0xMartin/TweenWave/Firmware/src/CommandLine.cpp

#include "CommandLine.h"

#include <SPIFFS.h>

CommandLine::CommandLine() {}

void CommandLine::RunSetup() {
  Serial.println(this->ascii_art);

  Serial.println(F("\n\n--------------------------------\n"));
  Serial.println(F("         ESP32 Marauder      \n"));
  Serial.println("            " + version_number + "\n");
  Serial.println(F("       By: justcallmekoko\n"));
  Serial.println(F("--------------------------------\n\n"));

  Serial.print("> ");
}

String CommandLine::getSerialInput() {
  String input = "";

  if (Serial.available() > 0)
    input = Serial.readStringUntil('\n');

  input.trim();
  return input;
}

void CommandLine::main(uint32_t currentTime) {
  String input = this->getSerialInput();

  this->runCommand(input);

  if (input != "")
    Serial.print("> ");
}

LinkedList<String> CommandLine::parseCommand(String input, char *delim) {
  LinkedList<String> cmd_args;

  bool inQuote = false;
  bool inApostrophe = false;
  String buffer = "";

  for (int i = 0; i < input.length(); i++) {
    char c = input.charAt(i);

    if (c == '"') {
      // Check if the quote is within an apostrophe
      if (inApostrophe) {
        buffer += c;
      } else {
        inQuote = !inQuote;
      }
    } else if (c == '\'') {
      // Check if the apostrophe is within a quote
      if (inQuote) {
        buffer += c;
      } else {
        inApostrophe = !inApostrophe;
      }
    } else if (!inQuote && !inApostrophe && strchr(delim, c) != NULL) {
      cmd_args.add(buffer);
      buffer = "";
    } else {
      buffer += c;
    }
  }

  // Add the last argument
  if (!buffer.isEmpty()) {
    cmd_args.add(buffer);
  }

  return cmd_args;
}

int CommandLine::argSearch(LinkedList<String> *cmd_args_list, String key) {
  for (int i = 0; i < cmd_args_list->size(); i++) {
    if (cmd_args_list->get(i) == key)
      return i;
  }

  return -1;
}

bool CommandLine::checkValueExists(LinkedList<String> *cmd_args_list,
                                   int index) {
  if (index < cmd_args_list->size() - 1)
    return true;

  return false;
}

bool CommandLine::inRange(int max, int index) {
  if ((index >= 0) && (index < max))
    return true;

  return false;
}

bool CommandLine::apSelected() {
  for (int i = 0; i < access_points->size(); i++) {
    if (access_points->get(i).selected)
      return true;
  }

  return false;
}

bool CommandLine::hasSSIDs() {
  if (ssids->size() == 0)
    return false;

  return true;
}

void CommandLine::showCounts(int selected, int unselected) {
  Serial.print((String)selected + " selected");

  if (unselected != -1)
    Serial.print(", " + (String)unselected + " unselected");

  Serial.println("");
}

String CommandLine::toLowerCase(String str) {
  String result = str;
  for (int i = 0; i < str.length(); i++) {
    int charValue = str.charAt(i);
    if (charValue >= 65 &&
        charValue <= 90) { // ASCII codes for uppercase letters
      charValue += 32;
      result.setCharAt(i, char(charValue));
    }
  }
  return result;
}

void CommandLine::filterAccessPoints(String filter) {
  int count_selected = 0;
  int count_unselected = 0;

  // Split the filter string into individual filters
  LinkedList<String> filters;
  int start = 0;
  int end = filter.indexOf(" or ");
  while (end != -1) {
    filters.add(filter.substring(start, end));
    start = end + 4;
    end = filter.indexOf(" or ", start);
  }
  filters.add(filter.substring(start));

  // Loop over each access point and check if it matches any of the filters
  for (int i = 0; i < access_points->size(); i++) {
    bool matchesFilter = false;
    for (int j = 0; j < filters.size(); j++) {
      String f = toLowerCase(filters.get(j));
      if (f.substring(0, 7) == "equals ") {
        String ssidEquals = f.substring(7);
        if ((ssidEquals.charAt(0) == '\"' &&
             ssidEquals.charAt(ssidEquals.length() - 1) == '\"' &&
             ssidEquals.length() > 1) ||
            (ssidEquals.charAt(0) == '\'' &&
             ssidEquals.charAt(ssidEquals.length() - 1) == '\'' &&
             ssidEquals.length() > 1)) {
          ssidEquals = ssidEquals.substring(1, ssidEquals.length() - 1);
        }
        if (access_points->get(i).essid.equalsIgnoreCase(ssidEquals)) {
          matchesFilter = true;
          break;
        }
      } else if (f.substring(0, 9) == "contains ") {
        String ssidContains = f.substring(9);
        if ((ssidContains.charAt(0) == '\"' &&
             ssidContains.charAt(ssidContains.length() - 1) == '\"' &&
             ssidContains.length() > 1) ||
            (ssidContains.charAt(0) == '\'' &&
             ssidContains.charAt(ssidContains.length() - 1) == '\'' &&
             ssidContains.length() > 1)) {
          ssidContains = ssidContains.substring(1, ssidContains.length() - 1);
        }
        String essid = toLowerCase(access_points->get(i).essid);
        if (essid.indexOf(ssidContains) != -1) {
          matchesFilter = true;
          break;
        }
      }
    }
    // Toggles the selected state of the AP
    AccessPoint new_ap = access_points->get(i);
    new_ap.selected = matchesFilter;
    access_points->set(i, new_ap);

    if (matchesFilter) {
      count_selected++;
    } else {
      count_unselected++;
    }
  }

  this->showCounts(count_selected, count_unselected);
}

void CommandLine::runCommand(String input) {
  if (input == "")
    return;

  if (wifi_scan_obj.scanning() &&
      wifi_scan_obj.currentScanMode == WIFI_SCAN_GPS_NMEA) {
    if (input != STOPSCAN_CMD)
      return;
  } else
    Serial.println("#" + input);

  LinkedList<String> cmd_args = this->parseCommand(input, " ");

  //// Admin commands
  // Help
  if (cmd_args.get(0) == HELP_CMD) {
    Serial.println(HELP_HEAD);
    Serial.println(HELP_CH_CMD);
    Serial.println(HELP_SETTINGS_CMD);
    Serial.println(HELP_CLEARAP_CMD_A);
    Serial.println(HELP_REBOOT_CMD);
    Serial.println(HELP_UPDATE_CMD_A);
    Serial.println(HELP_LS_CMD);
    Serial.println(HELP_LED_CMD);
    Serial.println(HELP_GPS_DATA_CMD);
    Serial.println(HELP_GPS_CMD);
    Serial.println(HELP_NMEA_CMD);

    // WiFi sniff/scan
    Serial.println(HELP_EVIL_PORTAL_CMD);
    Serial.println(HELP_KARMA_CMD);
    Serial.println(HELP_PACKET_COUNT_CMD);
    Serial.println(HELP_PING_CMD);
    Serial.println(HELP_ARP_SCAN_CMD);
    Serial.println(HELP_PORT_SCAN_CMD);
    Serial.println(HELP_SIGSTREN_CMD);
    Serial.println(HELP_SCAN_ALL_CMD);
    Serial.println(HELP_SCANAP_CMD);
    Serial.println(HELP_SCANSTA_CMD);
    Serial.println(HELP_SNIFF_RAW_CMD);
    Serial.println(HELP_SNIFF_BEACON_CMD);
    Serial.println(HELP_SNIFF_PROBE_CMD);
    Serial.println(HELP_SNIFF_PWN_CMD);
    Serial.println(HELP_SNIFF_PINESCAN_CMD);
    Serial.println(HELP_SNIFF_MULTISSID_CMD);
    Serial.println(HELP_SNIFF_ESP_CMD);
    Serial.println(HELP_SNIFF_DEAUTH_CMD);
    Serial.println(HELP_SNIFF_PMKID_CMD);
    Serial.println(HELP_STOPSCAN_CMD);
#ifdef HAS_GPS
    Serial.println(HELP_WARDRIVE_CMD);
#endif

    // WiFi attack
    Serial.println(HELP_ATTACK_CMD);

    // WiFi Aux
    Serial.println(HELP_INFO_CMD);
    Serial.println(HELP_LIST_AP_CMD_A);
    Serial.println(HELP_LIST_AP_CMD_B);
    Serial.println(HELP_LIST_AP_CMD_C);
    Serial.println(HELP_LIST_AP_CMD_D);
    Serial.println(HELP_LIST_AP_CMD_E);
    Serial.println(HELP_LIST_AP_CMD_F);
    Serial.println(HELP_SEL_CMD_A);
    Serial.println(HELP_SSID_CMD_A);
    Serial.println(HELP_SSID_CMD_B);
    Serial.println(HELP_SAVE_CMD);
    Serial.println(HELP_LOAD_CMD);
    Serial.println(HELP_JOIN_CMD);

// Bluetooth sniff/scan
#ifdef HAS_BT
    Serial.println(HELP_BT_SNIFF_CMD);
    Serial.println(HELP_BT_SPAM_CMD);
    Serial.println(HELP_BT_SPOOFAT_CMD);
// Serial.println(HELP_BT_SWIFTPAIR_SPAM_CMD);
// Serial.println(HELP_BT_SAMSUNG_SPAM_CMD);
// Serial.println(HELP_BT_SPAM_ALL_CMD);
#ifdef HAS_GPS
    Serial.println(HELP_BT_WARDRIVE_CMD);
#endif
    Serial.println(HELP_BT_SKIM_CMD);
#endif
    Serial.println(HELP_FOOT);
    return;
  }

  // Stop Scan
  if (cmd_args.get(0) == STOPSCAN_CMD) {
    // if (wifi_scan_obj.currentScanMode == OTA_UPDATE) {
    //   wifi_scan_obj.currentScanMode = WIFI_SCAN_OFF;
    // #ifdef HAS_SCREEN
    //   menu_function_obj.changeMenu(menu_function_obj.updateMenu.parentMenu);
    // #endif
    //  WiFi.softAPdisconnect(true);
    //  web_obj.shutdownServer();
    //  return;
    //}

    int f_arg = this->argSearch(&cmd_args, "-f");

    uint8_t old_scan_mode = wifi_scan_obj.currentScanMode;

    if (f_arg != -1) {
      WiFi.disconnect(true);
      delay(100);
    }

    wifi_scan_obj.StartScan(WIFI_SCAN_OFF);

    if (old_scan_mode == WIFI_SCAN_GPS_NMEA)
      Serial.println("END OF NMEA STREAM");
    else if (old_scan_mode == WIFI_SCAN_GPS_DATA)
      Serial.println("Stopping GPS data updates");
    else
      Serial.println("Stopping WiFi tran/recv");

// If we don't do this, the text and button coordinates will be off
#ifdef HAS_SCREEN
    display_obj.tft.init();
    menu_function_obj.changeMenu(menu_function_obj.current_menu);
#endif
  } else if (cmd_args.get(0) == GPS_DATA_CMD) {
#ifdef HAS_GPS
    if (gps_obj.getGpsModuleStatus()) {
      Serial.println("Getting GPS Data. Stop with " + (String)STOPSCAN_CMD);
      wifi_scan_obj.currentScanMode = WIFI_SCAN_GPS_DATA;
#ifdef HAS_SCREEN
      menu_function_obj.changeMenu(&menu_function_obj.gpsInfoMenu);
#endif
      wifi_scan_obj.StartScan(WIFI_SCAN_GPS_DATA, TFT_CYAN);
    }
#endif
  } else if (cmd_args.get(0) == GPS_CMD) {
#ifdef HAS_GPS
    if (gps_obj.getGpsModuleStatus()) {
      int get_arg = this->argSearch(&cmd_args, "-g");
      int track_arg = this->argSearch(&cmd_args, "-t");
      int nmea_arg = this->argSearch(&cmd_args, "-n");

      if (get_arg != -1) {
        String gps_info = cmd_args.get(get_arg + 1);

        if (gps_info == "fix")
          Serial.println("Fix: " + gps_obj.getFixStatusAsString());
        else if (gps_info == "sat")
          Serial.println("Sats: " + gps_obj.getNumSatsString());
        else if (gps_info == "lat")
          Serial.println("Lat: " + gps_obj.getLat());
        else if (gps_info == "lon")
          Serial.println("Lon: " + gps_obj.getLon());
        else if (gps_info == "alt")
          Serial.println("Alt: " + (String)gps_obj.getAlt());
        else if (gps_info == "accuracy")
          Serial.println("Accuracy: " + (String)gps_obj.getAccuracy());
        else if (gps_info == "date")
          Serial.println("Date/Time: " + gps_obj.getDatetime());
        else if (gps_info == "text") {
          Serial.println(gps_obj.getText());
        } else if (gps_info == "nmea") {
          int notparsed_arg = this->argSearch(&cmd_args, "-p");
          int notimp_arg = this->argSearch(&cmd_args, "-i");
          int recd_arg = this->argSearch(&cmd_args, "-r");
          if (notparsed_arg == -1 && notimp_arg == -1 && recd_arg == -1) {
            gps_obj.sendSentence(Serial, gps_obj.generateGXgga().c_str());
            gps_obj.sendSentence(Serial, gps_obj.generateGXrmc().c_str());
          } else if (notparsed_arg == -1 && notimp_arg == -1)
            Serial.println(gps_obj.getNmea());
          else if (notparsed_arg == -1)
            Serial.println(gps_obj.getNmeaNotimp());
          else
            Serial.println(gps_obj.getNmeaNotparsed());
        } else
          Serial.println("You did not provide a valid argument");
      } else if (nmea_arg != -1) {
        String nmea_type = cmd_args.get(nmea_arg + 1);

        if (nmea_type == "native" || nmea_type == "all" || nmea_type == "gps" ||
            nmea_type == "glonass" || nmea_type == "galileo" ||
            nmea_type == "navic" || nmea_type == "qzss" ||
            nmea_type == "beidou") {
          if (nmea_type == "beidou") {
            int beidou_bd_arg = this->argSearch(&cmd_args, "-b");
            if (beidou_bd_arg != -1)
              nmea_type = "beidou_bd";
          }
          gps_obj.setType(nmea_type);
          Serial.println("GPS Output Type Set To: " + nmea_type);
        } else
          Serial.println("You did not provide a valid argument");
      } else if (track_arg != -1) {
        wifi_scan_obj.currentScanMode = GPS_TRACKER;
#ifdef HAS_SCREEN
        menu_function_obj.changeMenu(&menu_function_obj.gpsInfoMenu);
#endif
        wifi_scan_obj.StartScan(GPS_TRACKER, TFT_CYAN);
      } else if (cmd_args.size() > 1)
        Serial.println("You did not provide a valid flag");
      else
        Serial.println("You did not provide an argument");
    }
#endif
  } else if (cmd_args.get(0) == NMEA_CMD) {
#ifdef HAS_GPS
    if (gps_obj.getGpsModuleStatus()) {
#ifdef HAS_SCREEN
      menu_function_obj.changeMenu(&menu_function_obj.gpsInfoMenu);
#endif
      Serial.println("NMEA STREAM FOLLOWS");
      wifi_scan_obj.currentScanMode = WIFI_SCAN_GPS_NMEA;
      wifi_scan_obj.StartScan(WIFI_SCAN_GPS_NMEA, TFT_CYAN);
    }
#endif
  }
  // LED command
  else if (cmd_args.get(0) == LED_CMD) {
    int hex_arg = this->argSearch(&cmd_args, "-s");
    int pat_arg = this->argSearch(&cmd_args, "-p");
#ifdef PIN
    if (hex_arg != -1) {
      String hexstring = cmd_args.get(hex_arg + 1);
      int number = (int)strtol(&hexstring[1], NULL, 16);
      int r = number >> 16;
      int g = number >> 8 & 0xFF;
      int b = number & 0xFF;
      // Serial.println(r);
      // Serial.println(g);
      // Serial.println(b);
      led_obj.setColor(r, g, b);
      led_obj.setMode(MODE_CUSTOM);
    } else if (pat_arg != -1) {
      String pat_name = cmd_args.get(pat_arg + 1);
      pat_name.toLowerCase();
      if (pat_name == "rainbow") {
        led_obj.setMode(MODE_RAINBOW);
      }
    }
#else
    Serial.println("This hardware does not support neopixel");
#endif
  }
  // ls command
  else if (cmd_args.get(0) == LS_CMD) {
#ifdef HAS_SD
    if (cmd_args.size() > 1)
      sd_obj.listDir(cmd_args.get(1));
    else
      Serial.println("You did not provide a dir to list");
#else
    Serial.println("SD support disabled, cannot use command");
    return;
#endif
  }

  // Channel command
  else if (cmd_args.get(0) == CH_CMD) {
    // Search for channel set arg
    int ch_set = this->argSearch(&cmd_args, "-s");

    if (cmd_args.size() == 1) {
      Serial.println("Current channel: " + (String)wifi_scan_obj.set_channel);
    } else if (ch_set != -1) {
      wifi_scan_obj.set_channel = cmd_args.get(ch_set + 1).toInt();
      wifi_scan_obj.changeChannel();
      Serial.println("Set channel: " + (String)wifi_scan_obj.set_channel);
    }
  }
  // Clear APs
  else if (cmd_args.get(0) == CLEARAP_CMD) {
    int ap_sw = this->argSearch(&cmd_args, "-a"); // APs
    int ss_sw = this->argSearch(&cmd_args, "-s"); // SSIDs
    int cl_sw = this->argSearch(&cmd_args, "-c"); // Stations

    if (ap_sw != -1) {
#ifdef HAS_SCREEN
      menu_function_obj.changeMenu(&menu_function_obj.clearAPsMenu);
#endif
      wifi_scan_obj.RunClearAPs();
    }

    if (ss_sw != -1) {
#ifdef HAS_SCREEN
      menu_function_obj.changeMenu(&menu_function_obj.clearSSIDsMenu);
#endif
      wifi_scan_obj.RunClearSSIDs();
    }

    if (cl_sw != -1) {
#ifdef HAS_SCREEN
      menu_function_obj.changeMenu(&menu_function_obj.clearAPsMenu);
#endif
      wifi_scan_obj.RunClearStations();
    }
  }

  else if (cmd_args.get(0) == SETTINGS_CMD) {
    int ss_sw = this->argSearch(&cmd_args, "-s");      // Set setting
    int re_sw = this->argSearch(&cmd_args, "-r");      // Reset setting
    int en_sw = this->argSearch(&cmd_args, "enable");  // enable setting
    int da_sw = this->argSearch(&cmd_args, "disable"); // disable setting

    if (re_sw != -1) {
      settings_obj.createDefaultSettings(SPIFFS);
      return;
    }

    if (ss_sw == -1) {
      settings_obj.printJsonSettings(settings_obj.getSettingsString());
    } else {
      bool result = false;
      String setting_name = cmd_args.get(ss_sw + 1);
      if (en_sw != -1)
        result = settings_obj.saveSetting<bool>(setting_name, true);
      else if (da_sw != -1)
        result = settings_obj.saveSetting<bool>(setting_name, false);
      else {
        Serial.println("You did not properly enable/disable this setting.");
        return;
      }

      if (!result) {
        Serial.println("Could not successfully update setting \"" +
                       setting_name + "\"");
        return;
      }
    }
  }

  else if (cmd_args.get(0) == REBOOT_CMD) {
    Serial.println("Rebooting...");
    ESP.restart();
  }

  //// WiFi/Bluetooth Scan/Attack commands
  if (!wifi_scan_obj.scanning()) {
    // Dump pcap/log to serial too, valid for all scan/attack commands
    wifi_scan_obj.save_serial = this->argSearch(&cmd_args, "-serial") != -1;

    // Signal strength scan
    if (cmd_args.get(0) == SIGSTREN_CMD) {
      Serial.println("Starting Signal Strength Scan. Stop with " +
                     (String)STOPSCAN_CMD);
#ifdef HAS_SCREEN
      display_obj.clearScreen();
      menu_function_obj.drawStatusBar();
#endif
      wifi_scan_obj.StartScan(WIFI_SCAN_SIG_STREN, TFT_MAGENTA);
      wifi_scan_obj.renderPacketRate();
    }
    // Packet count
    else if (cmd_args.get(0) == PACKET_COUNT_CMD) {
      Serial.println("Starting Packet Count Scan. Stop with " +
                     (String)STOPSCAN_CMD);
#ifdef HAS_SCREEN
      display_obj.clearScreen();
      menu_function_obj.drawStatusBar();
#endif
      wifi_scan_obj.StartScan(WIFI_SCAN_PACKET_RATE, TFT_ORANGE);
    }
    // Wardrive
    else if (cmd_args.get(0) == WARDRIVE_CMD) {
#ifdef HAS_GPS
      if (gps_obj.getGpsModuleStatus()) {
        int sta_sw = this->argSearch(&cmd_args, "-s");

        if (sta_sw == -1) {
          Serial.println("Starting Wardrive. Stop with " +
                         (String)STOPSCAN_CMD);
#ifdef HAS_SCREEN
          display_obj.clearScreen();
          menu_function_obj.drawStatusBar();
#endif
          wifi_scan_obj.StartScan(WIFI_SCAN_WAR_DRIVE, TFT_GREEN);
        } else {
          Serial.println("Starting Station Wardrive. Stop with " +
                         (String)STOPSCAN_CMD);
#ifdef HAS_SCREEN
          display_obj.clearScreen();
          menu_function_obj.drawStatusBar();
#endif
          wifi_scan_obj.StartScan(WIFI_SCAN_STATION_WAR_DRIVE, TFT_GREEN);
        }
      } else
        Serial.println("GPS Module not detected");
#else
      Serial.println("GPS not supported");
#endif
    }
    // Karma
    else if (cmd_args.get(0) == KARMA_CMD) {
      int pr_sw = this->argSearch(&cmd_args, "-p");

      if (pr_sw == -1) {
        Serial.println("You did not provide a target index");
        return;
      }

      int pr_index = cmd_args.get(pr_sw + 1).toInt();

      if ((pr_index < 0) || (pr_index > probe_req_ssids->size() - 1)) {
        Serial.println("The provided index was not in range");
        return;
      }

      if (evil_portal_obj.setAP(probe_req_ssids->get(pr_index).essid)) {
        Serial.println("Starting Karma Attack with " +
                       probe_req_ssids->get(pr_index).essid + ". Stop with " +
                       (String)STOPSCAN_CMD);
#ifdef HAS_SCREEN
        display_obj.clearScreen();
        menu_function_obj.drawStatusBar();
#endif
        wifi_scan_obj.StartScan(WIFI_SCAN_EVIL_PORTAL, TFT_ORANGE);
        wifi_scan_obj.setMac();
      } else {
        Serial.println("Unable to set AP ESSID");
        return;
      }

    }
    // AP Scan
    else if (cmd_args.get(0) == EVIL_PORTAL_CMD) {
      int cmd_sw = this->argSearch(&cmd_args, "-c");
      int html_sw = this->argSearch(&cmd_args, "-w");

      if (cmd_sw != -1) {
        String et_command = cmd_args.get(cmd_sw + 1);
        if (et_command == "start") {
          Serial.println("Starting Evil Portal. Stop with " +
                         (String)STOPSCAN_CMD);
#ifdef HAS_SCREEN
          display_obj.clearScreen();
          menu_function_obj.drawStatusBar();
#endif
          if (html_sw != -1) {
            String target_html_name = cmd_args.get(html_sw + 1);
            evil_portal_obj.target_html_name = target_html_name;
            evil_portal_obj.using_serial_html = false;
            Serial.println("Set html file as " +
                           evil_portal_obj.target_html_name);
          }
          // else {
          //   evil_portal_obj.target_html_name = "index.html";
          // }
          wifi_scan_obj.StartScan(WIFI_SCAN_EVIL_PORTAL, TFT_MAGENTA);
        } else if (et_command == "reset") {

        } else if (et_command == "ack") {

        } else if (et_command == "sethtml") {
          String target_html_name = cmd_args.get(cmd_sw + 2);
          evil_portal_obj.target_html_name = target_html_name;
          evil_portal_obj.using_serial_html = false;
          Serial.println("Set html file as " +
                         evil_portal_obj.target_html_name);
        } else if (et_command == "sethtmlstr") {
          evil_portal_obj.setHtmlFromSerial();
        } else if (et_command == "setap") {
          int target_ap_index = cmd_args.get(cmd_sw + 2).toInt();
          if ((target_ap_index >= 0) &&
              (target_ap_index < access_points->size())) {
            evil_portal_obj.setAP(access_points->get(target_ap_index).essid);
            AccessPoint new_ap = access_points->get(target_ap_index);
            new_ap.selected = true;
            access_points->set(target_ap_index, new_ap);

            evil_portal_obj.ap_index = target_ap_index;
          }
        }
      }
    } else if (cmd_args.get(0) == SCAN_ALL_CMD) {
      Serial.println("Scanning for APs and Stations. Stop with " +
                     (String)STOPSCAN_CMD);
      wifi_scan_obj.StartScan(WIFI_SCAN_AP_STA, TFT_MAGENTA);
    } else if (cmd_args.get(0) == SCANAP_CMD) {
      int full_sw = -1;
#ifdef HAS_SCREEN
      display_obj.clearScreen();
      menu_function_obj.drawStatusBar();
#endif

      if (full_sw == -1) {
        Serial.println("Starting AP scan. Stop with " + (String)STOPSCAN_CMD);
        wifi_scan_obj.StartScan(WIFI_SCAN_TARGET_AP, TFT_MAGENTA);
      } else {
        Serial.println("Starting Full AP scan. Stop with " +
                       (String)STOPSCAN_CMD);
        wifi_scan_obj.StartScan(WIFI_SCAN_TARGET_AP_FULL, TFT_MAGENTA);
      }
    }
    // Raw sniff
    else if (cmd_args.get(0) == SNIFF_RAW_CMD) {
      Serial.println("Starting Raw sniff. Stop with " + (String)STOPSCAN_CMD);
#ifdef HAS_SCREEN
      display_obj.clearScreen();
      menu_function_obj.drawStatusBar();
#endif
      wifi_scan_obj.StartScan(WIFI_SCAN_RAW_CAPTURE, TFT_WHITE);
    }
    // Scan stations
    else if (cmd_args.get(0) == SCANSTA_CMD) {
      if (access_points->size() < 1)
        Serial.println("The AP list is empty. Scan APs first with " +
                       (String)SCANAP_CMD);

      Serial.println("Starting Station scan. Stop with " +
                     (String)STOPSCAN_CMD);
#ifdef HAS_SCREEN
      display_obj.clearScreen();
      menu_function_obj.drawStatusBar();
#endif
      wifi_scan_obj.StartScan(WIFI_SCAN_STATION, TFT_ORANGE);
    }
    // Beacon sniff
    else if (cmd_args.get(0) == SNIFF_BEACON_CMD) {
      Serial.println("Starting Beacon sniff. Stop with " +
                     (String)STOPSCAN_CMD);
#ifdef HAS_SCREEN
      display_obj.clearScreen();
      menu_function_obj.drawStatusBar();
#endif
      wifi_scan_obj.StartScan(WIFI_SCAN_AP, TFT_MAGENTA);
    }
    // Probe sniff
    else if (cmd_args.get(0) == SNIFF_PROBE_CMD) {
      Serial.println("Starting Probe sniff. Stop with " + (String)STOPSCAN_CMD);
#ifdef HAS_SCREEN
      display_obj.clearScreen();
      menu_function_obj.drawStatusBar();
#endif
      wifi_scan_obj.StartScan(WIFI_SCAN_PROBE, TFT_MAGENTA);
    }
    // Deauth sniff
    else if (cmd_args.get(0) == SNIFF_DEAUTH_CMD) {
      Serial.println("Starting Deauth sniff. Stop with " +
                     (String)STOPSCAN_CMD);
#ifdef HAS_SCREEN
      display_obj.clearScreen();
      menu_function_obj.drawStatusBar();
#endif
      wifi_scan_obj.StartScan(WIFI_SCAN_DEAUTH, TFT_RED);
    }
    // Pwn sniff
    else if (cmd_args.get(0) == SNIFF_PWN_CMD) {
      Serial.println("Starting Pwnagotchi sniff. Stop with " +
                     (String)STOPSCAN_CMD);
#ifdef HAS_SCREEN
      display_obj.clearScreen();
      menu_function_obj.drawStatusBar();
#endif
      wifi_scan_obj.StartScan(WIFI_SCAN_PWN, TFT_MAGENTA);
    }
    // PineScan sniff
    else if (cmd_args.get(0) == SNIFF_PINESCAN_CMD) {
      Serial.println("Starting Pinescan sniff. Stop with " +
                     (String)STOPSCAN_CMD);
#ifdef HAS_SCREEN
      display_obj.clearScreen();
      menu_function_obj.drawStatusBar();
#endif
      wifi_scan_obj.StartScan(WIFI_SCAN_PINESCAN, TFT_MAGENTA);
    }
    // MultiSSID sniff
    else if (cmd_args.get(0) == SNIFF_MULTISSID_CMD) {
      Serial.println("Starting MultiSSID sniff. Stop with " +
                     (String)STOPSCAN_CMD);
#ifdef HAS_SCREEN
      display_obj.clearScreen();
      menu_function_obj.drawStatusBar();
#endif
      wifi_scan_obj.StartScan(WIFI_SCAN_MULTISSID, TFT_MAGENTA);
    }
    // Espressif sniff
    else if (cmd_args.get(0) == SNIFF_ESP_CMD) {
      Serial.println("Starting Espressif device sniff. Stop with " +
                     (String)STOPSCAN_CMD);
#ifdef HAS_SCREEN
      display_obj.clearScreen();
      menu_function_obj.drawStatusBar();
#endif
      wifi_scan_obj.StartScan(WIFI_SCAN_ESPRESSIF, TFT_MAGENTA);
    }
    // PMKID sniff
    else if (cmd_args.get(0) == SNIFF_PMKID_CMD) {
      int ch_sw = this->argSearch(&cmd_args, "-c");
      int d_sw = this->argSearch(&cmd_args, "-d"); // Deauth for pmkid
      int l_sw = this->argSearch(&cmd_args, "-l"); // Only run on list

      if (l_sw != -1) {
        if (!this->apSelected()) {
          Serial.println("You don't have any targets selected. Use " +
                         (String)SEL_CMD);
          return;
        }
      }

      if (ch_sw != -1) {
        wifi_scan_obj.set_channel = cmd_args.get(ch_sw + 1).toInt();
        wifi_scan_obj.changeChannel();
        Serial.println("Set channel: " + (String)wifi_scan_obj.set_channel);
      }

      if (d_sw == -1) {
        Serial.println("Starting PMKID sniff on channel " +
                       (String)wifi_scan_obj.set_channel + ". Stop with " +
                       (String)STOPSCAN_CMD);
        wifi_scan_obj.StartScan(WIFI_SCAN_EAPOL, TFT_VIOLET);
      } else if ((d_sw != -1) && (l_sw != -1)) {
        Serial.println(
            "Starting TARGETED PMKID sniff with deauthentication on channel " +
            (String)wifi_scan_obj.set_channel + ". Stop with " +
            (String)STOPSCAN_CMD);
        wifi_scan_obj.StartScan(WIFI_SCAN_ACTIVE_LIST_EAPOL, TFT_VIOLET);
      } else {
        Serial.println(
            "Starting PMKID sniff with deauthentication on channel " +
            (String)wifi_scan_obj.set_channel + ". Stop with " +
            (String)STOPSCAN_CMD);
        wifi_scan_obj.StartScan(WIFI_SCAN_ACTIVE_EAPOL, TFT_VIOLET);
      }
    }

    //// WiFi attack commands
    // attack
    if (cmd_args.get(0) == ATTACK_CMD) {
      int attack_type_switch = this->argSearch(&cmd_args, "-t"); // Required
      int list_beacon_sw = this->argSearch(&cmd_args, "-l");
      int rand_beacon_sw = this->argSearch(&cmd_args, "-r");
      int ap_beacon_sw = this->argSearch(&cmd_args, "-a");
      int src_addr_sw = this->argSearch(&cmd_args, "-s");
      int dst_addr_sw = this->argSearch(&cmd_args, "-d");
      int targ_sw = this->argSearch(&cmd_args, "-c");

      if (attack_type_switch == -1) {
        Serial.println("You must specify an attack type");
        return;
      } else {
        String attack_type = cmd_args.get(attack_type_switch + 1);

        // Branch on attack type
        // Deauth
        if (attack_type == ATTACK_TYPE_DEAUTH) {
          // Default to broadcast
          if ((dst_addr_sw == -1) && (targ_sw == -1)) {
            Serial.println("Sending to broadcast...");
            wifi_scan_obj.dst_mac = "ff:ff:ff:ff:ff:ff";
          }
          // Dest addr specified
          else if (dst_addr_sw != -1) {
            wifi_scan_obj.dst_mac = cmd_args.get(dst_addr_sw + 1);
            Serial.println("Sending to " + wifi_scan_obj.dst_mac + "...");
          }
          // Station list specified
          else if (targ_sw != -1)
            Serial.println("Sending to Station list");

          // Source addr not specified
          if (src_addr_sw == -1) {
            if (!this->apSelected()) {
              Serial.println("You don't have any targets selected. Use " +
                             (String)SEL_CMD);
              return;
            }
#ifdef HAS_SCREEN
            display_obj.clearScreen();
            menu_function_obj.drawStatusBar();
#endif
            Serial.println("Starting Deauthentication attack. Stop with " +
                           (String)STOPSCAN_CMD);
            // Station list not specified
            if (targ_sw == -1)
              wifi_scan_obj.StartScan(WIFI_ATTACK_DEAUTH, TFT_RED);
            // Station list specified
            else
              wifi_scan_obj.StartScan(WIFI_ATTACK_DEAUTH_TARGETED, TFT_ORANGE);
          }
          // Source addr specified
          else {
            String src_mac_str = cmd_args.get(src_addr_sw + 1);
            sscanf(src_mac_str.c_str(), "%2hhx:%2hhx:%2hhx:%2hhx:%2hhx:%2hhx",
                   &wifi_scan_obj.src_mac[0], &wifi_scan_obj.src_mac[1],
                   &wifi_scan_obj.src_mac[2], &wifi_scan_obj.src_mac[3],
                   &wifi_scan_obj.src_mac[4], &wifi_scan_obj.src_mac[5]);

#ifdef HAS_SCREEN
            display_obj.clearScreen();
            menu_function_obj.drawStatusBar();
#endif
            Serial.println(
                "Starting Manual Deauthentication attack. Stop with " +
                (String)STOPSCAN_CMD);
            wifi_scan_obj.StartScan(WIFI_ATTACK_DEAUTH_MANUAL, TFT_RED);
          }
        }
        // Bad Msg
        else if (attack_type == ATTACK_TYPE_BM) {
          // Attack all
          if (targ_sw == -1) {
            Serial.println(
                "Starting Bad Msg attack against all stations. Stop with " +
                (String)STOPSCAN_CMD);
#ifdef HAS_SCREEN
            display_obj.clearScreen();
            menu_function_obj.drawStatusBar();
#endif
            wifi_scan_obj.StartScan(WIFI_ATTACK_BAD_MSG, TFT_RED);
          }
          // Target clients
          else {
            Serial.println("Starting targeted Bad Msg attack. Stop with " +
                           (String)STOPSCAN_CMD);
#ifdef HAS_SCREEN
            display_obj.clearScreen();
            menu_function_obj.drawStatusBar();
#endif
            wifi_scan_obj.StartScan(WIFI_ATTACK_BAD_MSG_TARGETED, TFT_YELLOW);
          }
        } else if (attack_type == ATTACK_TYPE_S) {
          // Attack all
          if (targ_sw == -1) {
            Serial.println(
                "Starting Sleep attack against all stations. Stop with " +
                (String)STOPSCAN_CMD);
#ifdef HAS_SCREEN
            display_obj.clearScreen();
            menu_function_obj.drawStatusBar();
#endif
            wifi_scan_obj.StartScan(WIFI_ATTACK_SLEEP, TFT_RED);
          }
          // Target clients
          else {
            Serial.println("Starting targeted Sleep attack. Stop with " +
                           (String)STOPSCAN_CMD);
#ifdef HAS_SCREEN
            display_obj.clearScreen();
            menu_function_obj.drawStatusBar();
#endif
            wifi_scan_obj.StartScan(WIFI_ATTACK_SLEEP_TARGETED, TFT_MAGENTA);
          }
        }
        // Beacon
        else if (attack_type == ATTACK_TYPE_BEACON) {
          // spam by list
          if (list_beacon_sw != -1) {
            if (!this->hasSSIDs()) {
              Serial.println("You don't have any SSIDs in your list. Use " +
                             (String)SSID_CMD);
              return;
            }
#ifdef HAS_SCREEN
            display_obj.clearScreen();
            menu_function_obj.drawStatusBar();
#endif
            Serial.println("Starting Beacon list spam. Stop with " +
                           (String)STOPSCAN_CMD);
            wifi_scan_obj.StartScan(WIFI_ATTACK_BEACON_LIST, TFT_RED);
          }
          // spam with random
          else if (rand_beacon_sw != -1) {
#ifdef HAS_SCREEN
            display_obj.clearScreen();
            menu_function_obj.drawStatusBar();
#endif
            Serial.println("Starting random Beacon spam. Stop with " +
                           (String)STOPSCAN_CMD);
            wifi_scan_obj.StartScan(WIFI_ATTACK_BEACON_SPAM, TFT_ORANGE);
          }
          // Spam from AP list
          else if (ap_beacon_sw != -1) {
            if (!this->apSelected()) {
              Serial.println("You don't have any targets selected. Use " +
                             (String)SEL_CMD);
              return;
            }
#ifdef HAS_SCREEN
            display_obj.clearScreen();
            menu_function_obj.drawStatusBar();
#endif
            Serial.println("Starting Targeted AP Beacon spam. Stop with " +
                           (String)STOPSCAN_CMD);
            wifi_scan_obj.StartScan(WIFI_ATTACK_AP_SPAM, TFT_MAGENTA);
          } else {
            Serial.println("You did not specify a beacon attack type");
          }
        } else if (attack_type == ATTACK_TYPE_PROBE) {
          if (!this->apSelected()) {
            Serial.println("You don't have any targets selected. Use " +
                           (String)SEL_CMD);
            return;
          }
          Serial.println("Starting Probe spam. Stop with " +
                         (String)STOPSCAN_CMD);
#ifdef HAS_SCREEN
          display_obj.clearScreen();
          menu_function_obj.drawStatusBar();
#endif
          wifi_scan_obj.StartScan(WIFI_ATTACK_AUTH, TFT_RED);
        } else if (attack_type == ATTACK_TYPE_RR) {
          Serial.println("Starting Rick Roll Beacon spam. Stop with " +
                         (String)STOPSCAN_CMD);
#ifdef HAS_SCREEN
          display_obj.clearScreen();
          menu_function_obj.drawStatusBar();
#endif
          wifi_scan_obj.StartScan(WIFI_ATTACK_RICK_ROLL, TFT_YELLOW);
        } else {
          Serial.println("Attack type not properly defined");
          return;
        }
      }
    }

    //// Bluetooth scan/attack commands
    // Bluetooth scan
    if (cmd_args.get(0) == BT_SNIFF_CMD) {
#ifdef HAS_BT
      int bt_type_sw = this->argSearch(&cmd_args, "-t");

      // Specifying type of bluetooth sniff
      if (bt_type_sw != -1) {
        String bt_type = cmd_args.get(bt_type_sw + 1);

        bt_type.toLowerCase();

        // Airtag sniff
        if (bt_type == "airtag") {
          Serial.println("Starting Airtag sniff. Stop with " +
                         (String)STOPSCAN_CMD);
#ifdef HAS_SCREEN
          display_obj.clearScreen();
          menu_function_obj.drawStatusBar();
#endif
          wifi_scan_obj.StartScan(BT_SCAN_AIRTAG, TFT_WHITE);
        } else if (bt_type == "flipper") {
          Serial.println("Starting Flipper sniff. Stop with " +
                         (String)STOPSCAN_CMD);
#ifdef HAS_SCREEN
          display_obj.clearScreen();
          menu_function_obj.drawStatusBar();
#endif
          wifi_scan_obj.StartScan(BT_SCAN_FLIPPER, TFT_ORANGE);
        }
      }
      // General bluetooth sniff
      else {
        Serial.println("Starting Bluetooth scan. Stop with " +
                       (String)STOPSCAN_CMD);
#ifdef HAS_SCREEN
        display_obj.clearScreen();
        menu_function_obj.drawStatusBar();
#endif
        wifi_scan_obj.StartScan(BT_SCAN_ALL, TFT_GREEN);
      }
#else
      Serial.println("Bluetooth not supported");
#endif
    } else if (cmd_args.get(0) == BT_SPOOFAT_CMD) {
      int at_sw = this->argSearch(&cmd_args, "-t");
      if (at_sw != -1) {
#ifdef HAS_BT
        int target_mac = cmd_args.get(at_sw + 1).toInt();
        if (target_mac < airtags->size()) {
          for (int i = 0; i < airtags->size(); i++) {
            AirTag at = airtags->get(i);
            if (i == target_mac)
              at.selected = true;
            else
              at.selected = false;
            airtags->set(i, at);
          }
          Serial.println("Spoofing Airtag: " + airtags->get(target_mac).mac);
#ifdef HAS_SCREEN
          display_obj.clearScreen();
          menu_function_obj.drawStatusBar();
#endif
          wifi_scan_obj.StartScan(BT_SPOOF_AIRTAG, TFT_WHITE);
        } else {
          Serial.println("Provided index is out of range: " +
                         (String)target_mac);
          return;
        }
#endif
      }
    } else if (cmd_args.get(0) == BT_SPAM_CMD) {
      int bt_type_sw = this->argSearch(&cmd_args, "-t");
      if (bt_type_sw != -1) {
        String bt_type = cmd_args.get(bt_type_sw + 1);

        if (bt_type == "apple") {
#ifdef HAS_BT
          Serial.println("Starting Sour Apple attack. Stop with " +
                         (String)STOPSCAN_CMD);
#ifdef HAS_SCREEN
          display_obj.clearScreen();
          menu_function_obj.drawStatusBar();
#endif
          wifi_scan_obj.StartScan(BT_ATTACK_SOUR_APPLE, TFT_GREEN);
#else
          Serial.println("Bluetooth not supported");
#endif
        } else if (bt_type == "windows") {
#ifdef HAS_BT
          Serial.println("Starting Swiftpair Spam attack. Stop with " +
                         (String)STOPSCAN_CMD);
#ifdef HAS_SCREEN
          display_obj.clearScreen();
          menu_function_obj.drawStatusBar();
#endif
          wifi_scan_obj.StartScan(BT_ATTACK_SWIFTPAIR_SPAM, TFT_CYAN);
#else
          Serial.println("Bluetooth not supported");
#endif
        } else if (bt_type == "samsung") {
#ifdef HAS_BT
          Serial.println("Starting Samsung Spam attack. Stop with " +
                         (String)STOPSCAN_CMD);
#ifdef HAS_SCREEN
          display_obj.clearScreen();
          menu_function_obj.drawStatusBar();
#endif
          wifi_scan_obj.StartScan(BT_ATTACK_SAMSUNG_SPAM, TFT_CYAN);
#else
          Serial.println("Bluetooth not supported");
#endif
        } else if (bt_type == "google") {
#ifdef HAS_BT
          Serial.println("Starting Google Spam attack. Stop with " +
                         (String)STOPSCAN_CMD);
#ifdef HAS_SCREEN
          display_obj.clearScreen();
          menu_function_obj.drawStatusBar();
#endif
          wifi_scan_obj.StartScan(BT_ATTACK_GOOGLE_SPAM, TFT_CYAN);
#else
          Serial.println("Bluetooth not supported");
#endif
        } else if (bt_type == "flipper") {
#ifdef HAS_BT
          Serial.println("Starting Flipper Spam attack. Stop with " +
                         (String)STOPSCAN_CMD);
#ifdef HAS_SCREEN
          display_obj.clearScreen();
          menu_function_obj.drawStatusBar();
#endif
          wifi_scan_obj.StartScan(BT_ATTACK_FLIPPER_SPAM, TFT_ORANGE);
#else
          Serial.println("Bluetooth not supported");
#endif
        } else if (bt_type == "all") {
#ifdef HAS_BT
          Serial.println("Starting BT Spam All attack. Stop with " +
                         (String)STOPSCAN_CMD);
#ifdef HAS_SCREEN
          display_obj.clearScreen();
          menu_function_obj.drawStatusBar();
#endif
          wifi_scan_obj.StartScan(BT_ATTACK_SPAM_ALL, TFT_MAGENTA);
#else
          Serial.println("Bluetooth not supported");
#endif
        } else {
          Serial.println("You did not specify a correct spam type");
        }
      }
    }
    // Wardrive
    else if (cmd_args.get(0) == BT_WARDRIVE_CMD) {
#ifdef HAS_BT
#ifdef HAS_GPS
      if (gps_obj.getGpsModuleStatus()) {
        int cont_sw = this->argSearch(&cmd_args, "-c");

        if (cont_sw == -1) {
          Serial.println("Starting BT Wardrive. Stop with " +
                         (String)STOPSCAN_CMD);
#ifdef HAS_SCREEN
          display_obj.clearScreen();
          menu_function_obj.drawStatusBar();
#endif
          wifi_scan_obj.StartScan(BT_SCAN_WAR_DRIVE, TFT_GREEN);
        } else {
          Serial.println("Starting Continuous BT Wardrive. Stop with " +
                         (String)STOPSCAN_CMD);
#ifdef HAS_SCREEN
          display_obj.clearScreen();
          menu_function_obj.drawStatusBar();
#endif
          wifi_scan_obj.StartScan(BT_SCAN_WAR_DRIVE_CONT, TFT_GREEN);
        }
      } else
        Serial.println("GPS Module not detected");
#else
      Serial.println("GPS not supported");
#endif
#else
      Serial.println("Bluetooth not supported");
#endif

    }
    // Bluetooth CC Skimmer scan
    else if (cmd_args.get(0) == BT_SKIM_CMD) {
#ifdef HAS_BT
      Serial.println("Starting Bluetooth CC Skimmer scan. Stop with " +
                     (String)STOPSCAN_CMD);
#ifdef HAS_SCREEN
      display_obj.clearScreen();
      menu_function_obj.drawStatusBar();
#endif
      wifi_scan_obj.StartScan(BT_SCAN_SKIMMERS, TFT_MAGENTA);
#else
      Serial.println("Bluetooth not supported");
#endif
    }

    // Update command
    if (cmd_args.get(0) == UPDATE_CMD) {
      // int w_sw = this->argSearch(&cmd_args, "-w"); // Web update
      int sd_sw = this->argSearch(&cmd_args, "-s"); // SD Update

      // Update via OTA
      // if (w_sw != -1) {
      //  Serial.println("Starting Marauder OTA Update. Stop with " +
      //  (String)STOPSCAN_CMD); wifi_scan_obj.currentScanMode = OTA_UPDATE;
      // #ifdef HAS_SCREEN
      //  menu_function_obj.changeMenu(menu_function_obj.updateMenu);
      // #endif
      //  web_obj.setupOTAupdate();
      //}
      // Update via SD
      if (sd_sw != -1) {
#ifdef HAS_SD
        if (!sd_obj.supported) {
          Serial.println("SD card is not connected. Cannot perform SD Update");
          return;
        }
        wifi_scan_obj.currentScanMode = OTA_UPDATE;
        sd_obj.runUpdate();
#else
        Serial.println("SD card support disabled. Cannot perform SD Update");
        return;
#endif
      }
    }
  }

  if (wifi_scan_obj.wifi_connected) {
    // Ping Scan
    if (cmd_args.get(0) == PING_CMD) {
      Serial.println("Starting Ping Scan. Stop with " + (String)STOPSCAN_CMD);
#ifdef HAS_SCREEN
      display_obj.clearScreen();
      menu_function_obj.drawStatusBar();
#endif
      wifi_scan_obj.StartScan(WIFI_PING_SCAN, TFT_GREEN);
    }

    if (cmd_args.get(0) == ARP_SCAN_CMD) {
      Serial.println("Starting ARP Scan. Stop with " + (String)STOPSCAN_CMD);
#ifdef HAS_SCREEN
      display_obj.clearScreen();
      menu_function_obj.drawStatusBar();
#endif
      wifi_scan_obj.StartScan(WIFI_ARP_SCAN, TFT_CYAN);
    }

    // Port Scan
    if (cmd_args.get(0) == PORT_SCAN_CMD) {
      int all_sw = this->argSearch(&cmd_args, "-a");
      int ip_sw = this->argSearch(&cmd_args, "-t");
      int port_sw = this->argSearch(&cmd_args, "-p");

      if (port_sw != -1)
        int ip_index = cmd_args.get(ip_sw + 1).toInt();

      // Check they specified ip index
      if (ip_sw != -1) {
        int ip_index = cmd_args.get(ip_sw + 1).toInt();

        // Check provided index is in list
        if (ip_index < ipList->size()) {

          // Full port scan
          if (all_sw != -1) {
            Serial.println("Selected: " + ipList->get(ip_index).toString());
            wifi_scan_obj.current_scan_ip = ipList->get(ip_index);
#ifdef HAS_SCREEN
            display_obj.clearScreen();
            menu_function_obj.drawStatusBar();
#endif
            wifi_scan_obj.StartScan(WIFI_PORT_SCAN_ALL, TFT_BLUE);
          }
        } else {
          Serial.println("The IP index specified is out of range");
          return;
        }
      } else if (port_sw != -1) {

      } else {
        Serial.println("You did not specify an IP index");
        return;
      }
    }
  }

  int count_selected = 0;
  //// WiFi aux commands
  // List access points
  if (cmd_args.get(0) == LIST_AP_CMD) {
    int ap_sw = this->argSearch(&cmd_args, "-a");
    int ss_sw = this->argSearch(&cmd_args, "-s");
    int cl_sw = this->argSearch(&cmd_args, "-c");
    int at_sw = this->argSearch(&cmd_args, "-t");
    int ip_sw = this->argSearch(&cmd_args, "-i");
    int pr_sw = this->argSearch(&cmd_args, "-p");

    // List APs
    if (ap_sw != -1) {
      for (int i = 0; i < access_points->size(); i++) {
        if (access_points->get(i).selected) {
          Serial.println("[" + (String)i +
                         "][CH:" + (String)access_points->get(i).channel +
                         "] " + access_points->get(i).essid + " " +
                         (String)access_points->get(i).rssi + " (selected)");
          count_selected += 1;
        } else
          Serial.println("[" + (String)i +
                         "][CH:" + (String)access_points->get(i).channel +
                         "] " + access_points->get(i).essid + " " +
                         (String)access_points->get(i).rssi);
      }
      this->showCounts(count_selected);
    }
    // List IPs
    else if (ip_sw != -1) {
      for (int i = 0; i < ipList->size(); i++) {
        Serial.println("[" + (String)i + "] " + ipList->get(i).toString());
      }
    }
    // List Probes
    else if (pr_sw != -1) {
      for (int i = 0; i < probe_req_ssids->size(); i++) {
        Serial.println("[" + (String)i + "] " + probe_req_ssids->get(i).essid);
      }
    }
    // List SSIDs
    else if (ss_sw != -1) {
      for (int i = 0; i < ssids->size(); i++) {
        if (ssids->get(i).selected) {
          Serial.println("[" + (String)i + "] " + ssids->get(i).essid +
                         " (selected)");
          count_selected += 1;
        } else
          Serial.println("[" + (String)i + "] " + ssids->get(i).essid);
      }
      this->showCounts(count_selected);
    }
    // List Stations
    else if (cl_sw != -1) {
      char sta_mac[] = "00:00:00:00:00:00";
      for (int x = 0; x < access_points->size(); x++) {
        Serial.println("[" + (String)x + "] " + access_points->get(x).essid +
                       " " + (String)access_points->get(x).rssi + ":");
        for (int i = 0; i < access_points->get(x).stations->size(); i++) {
          wifi_scan_obj.getMAC(
              sta_mac,
              stations->get(access_points->get(x).stations->get(i)).mac, 0);
          if (stations->get(access_points->get(x).stations->get(i)).selected) {
            Serial.print("  [" +
                         (String)access_points->get(x).stations->get(i) + "] ");
            Serial.print(sta_mac);
            Serial.println(" (selected)");
            count_selected += 1;
          } else {
            Serial.print("  [" +
                         (String)access_points->get(x).stations->get(i) + "] ");
            Serial.println(sta_mac);
          }
        }
      }
      this->showCounts(count_selected);
    }
    // List airtags
    else if (at_sw != -1) {
      for (int i = 0; i < airtags->size(); i++) {
        Serial.println("[" + (String)i + "]MAC: " + airtags->get(i).mac);
      }
    } else {
      Serial.println("You did not specify which list to show");
      return;
    }
  } else if (cmd_args.get(0) == INFO_CMD) {
    int ap_sw = this->argSearch(&cmd_args, "-a");

    if (ap_sw != -1) {
      int filter_ap = cmd_args.get(ap_sw + 1).toInt();
      wifi_scan_obj.RunAPInfo(filter_ap, false);
    } else {
      wifi_scan_obj.currentScanMode = SHOW_INFO;
#ifdef HAS_SCREEN
      menu_function_obj.changeMenu(&menu_function_obj.infoMenu);
#endif
      wifi_scan_obj.RunInfo();
    }
  } else if (cmd_args.get(0) == JOIN_CMD) {
    int ap_sw = this->argSearch(&cmd_args, "-a");
    int pw_sw = this->argSearch(&cmd_args, "-p");
    int s_sw = this->argSearch(&cmd_args, "-s");

    if ((ap_sw != -1) && (pw_sw != -1)) {
      int index = cmd_args.get(ap_sw + 1).toInt();
      String password = cmd_args.get(pw_sw + 1);
      Serial.println("Using SSID: " + (String)access_points->get(index).essid +
                     " Password: " + (String)password);
      // wifi_scan_obj.currentScanMode = LV_JOIN_WIFI;
      // wifi_scan_obj.StartScan(LV_JOIN_WIFI, TFT_YELLOW);
      wifi_scan_obj.joinWiFi(access_points->get(index).essid, password, false);
#ifdef HAS_SCREEN
#ifdef HAS_MINI_KB
      menu_function_obj.changeMenu(menu_function_obj.current_menu);
#endif
#endif
    } else if (s_sw != -1) {
      String ssid = settings_obj.loadSetting<String>("ClientSSID");
      String pw = settings_obj.loadSetting<String>("ClientPW");

      if ((ssid != "") && (pw != "")) {
        wifi_scan_obj.joinWiFi(ssid, pw, false);
#ifdef HAS_SCREEN
        menu_function_obj.changeMenu(menu_function_obj.current_menu);
#endif
      } else {
        Serial.println("There are no saved WiFi credentials");
      }
    } else {
      Serial.println("You did not provide the proper args");
      return;
    }
  }
  // Select access points or stations
  else if (cmd_args.get(0) == SEL_CMD) {
    // Get switches
    int ap_sw = this->argSearch(&cmd_args, "-a");
    int ss_sw = this->argSearch(&cmd_args, "-s");
    int cl_sw = this->argSearch(&cmd_args, "-c");
    int filter_sw = this->argSearch(&cmd_args, "-f");

    count_selected = 0;
    int count_unselected = 0;
    // select Access points
    if (ap_sw != -1) {

      // If the filters parameter was specified
      if (filter_sw != -1) {
        String filter_ap = cmd_args.get(filter_sw + 1);
        this->filterAccessPoints(filter_ap);
      } else {
        // Get list of indices
        LinkedList<String> ap_index =
            this->parseCommand(cmd_args.get(ap_sw + 1), ",");

        // Select ALL APs
        if (cmd_args.get(ap_sw + 1) == "all") {
          for (int i = 0; i < access_points->size(); i++) {
            if (access_points->get(i).selected) {
              // Unselect "selected" ap
              AccessPoint new_ap = access_points->get(i);
              new_ap.selected = false;
              access_points->set(i, new_ap);
              count_unselected += 1;
            } else {
              // Select "unselected" ap
              AccessPoint new_ap = access_points->get(i);
              new_ap.selected = true;
              access_points->set(i, new_ap);
              count_selected += 1;
            }
          }
          this->showCounts(count_selected, count_unselected);
        }
        // Select specific APs
        else {
          // Mark APs as selected
          for (int i = 0; i < ap_index.size(); i++) {
            int index = ap_index.get(i).toInt();
            if (!this->inRange(access_points->size(), index)) {
              Serial.println("Index not in range: " + (String)index);
              continue;
            }
            if (access_points->get(index).selected) {
              // Unselect "selected" ap
              AccessPoint new_ap = access_points->get(index);
              new_ap.selected = false;
              access_points->set(index, new_ap);
              count_unselected += 1;
            } else {
              // Select "unselected" ap
              AccessPoint new_ap = access_points->get(index);
              new_ap.selected = true;
              access_points->set(index, new_ap);
              count_selected += 1;
            }
          }
          this->showCounts(count_selected, count_unselected);
        }
      }
    } else if (cl_sw != -1) {
      LinkedList<String> sta_index =
          this->parseCommand(cmd_args.get(cl_sw + 1), ",");

      // Select all Stations
      if (cmd_args.get(cl_sw + 1) == "all") {
        for (int i = 0; i < stations->size(); i++) {
          if (stations->get(i).selected) {
            // Unselect "selected" ap
            Station new_sta = stations->get(i);
            new_sta.selected = false;
            stations->set(i, new_sta);
            count_unselected += 1;
          } else {
            // Select "unselected" ap
            Station new_sta = stations->get(i);
            new_sta.selected = true;
            stations->set(i, new_sta);
            count_selected += 1;
          }
        }
        this->showCounts(count_selected, count_unselected);
      }
      // Select specific Stations
      else {
        // Mark Stations as selected
        for (int i = 0; i < sta_index.size(); i++) {
          int index = sta_index.get(i).toInt();
          if (!this->inRange(stations->size(), index)) {
            Serial.println("Index not in range: " + (String)index);
            continue;
          }
          if (stations->get(index).selected) {
            // Unselect "selected" ap
            Station new_sta = stations->get(index);
            new_sta.selected = false;
            stations->set(index, new_sta);
            count_unselected += 1;
          } else {
            // Select "unselected" ap
            Station new_sta = stations->get(index);
            new_sta.selected = true;
            stations->set(index, new_sta);
            count_selected += 1;
          }
        }
        this->showCounts(count_selected, count_unselected);
      }
    }
    // select ssids
    else if (ss_sw != -1) {
      // Get list of indices
      LinkedList<String> ss_index =
          this->parseCommand(cmd_args.get(ss_sw + 1), ",");

      // Select ALL SSIDs
      if (cmd_args.get(ss_sw + 1) == "all") {
        for (int i = 0; i < ssids->size(); i++) {
          if (ssids->get(i).selected) {
            ssid new_ssid = ssids->get(i);
            new_ssid.selected = false;
            ssids->set(i, new_ssid);
            count_unselected += 1;
          } else {
            ssid new_ssid = ssids->get(i);
            new_ssid.selected = true;
            ssids->set(i, new_ssid);
            count_selected += 1;
          }
        }
      } else {
        // Mark SSIDs as selected
        for (int i = 0; i < ss_index.size(); i++) {
          int index = ss_index.get(i).toInt();
          if (!this->inRange(ssids->size(), index)) {
            Serial.println("Index not in range: " + (String)index);
            continue;
          }
          if (ssids->get(index).selected) {
            ssid new_ssid = ssids->get(index);
            new_ssid.selected = false;
            ssids->set(index, new_ssid);
            count_unselected += 1;
          } else {
            ssid new_ssid = ssids->get(index);
            new_ssid.selected = true;
            ssids->set(index, new_ssid);
            count_selected += 1;
          }
        }
      }
      this->showCounts(count_selected, count_unselected);
    } else {
      Serial.println("You did not specify which list to select from");
      return;
    }
  } else if (cmd_args.get(0) == SAVE_CMD) {
    int ap_sw = this->argSearch(&cmd_args, "-a");
    int st_sw = this->argSearch(&cmd_args, "-s");

    if (ap_sw != -1) {
#ifdef HAS_SCREEN
      menu_function_obj.changeMenu(&menu_function_obj.saveAPsMenu);
#endif
      wifi_scan_obj.RunSaveAPList(true);
    } else if (st_sw != -1) {
#ifdef HAS_SCREEN
      menu_function_obj.changeMenu(&menu_function_obj.saveSSIDsMenu);
#endif
      wifi_scan_obj.RunSaveSSIDList(true);
    }
  } else if (cmd_args.get(0) == LOAD_CMD) {
    int ap_sw = this->argSearch(&cmd_args, "-a");
    int st_sw = this->argSearch(&cmd_args, "-s");

    if (ap_sw != -1) {
#ifdef HAS_SCREEN
      menu_function_obj.changeMenu(&menu_function_obj.loadAPsMenu);
#endif
      wifi_scan_obj.RunLoadAPList();
    } else if (st_sw != -1) {
#ifdef HAS_SCREEN
      menu_function_obj.changeMenu(&menu_function_obj.loadSSIDsMenu);
#endif
      wifi_scan_obj.RunLoadSSIDList();
    }
  }

  // SSID stuff
  else if (cmd_args.get(0) == SSID_CMD) {
    int add_sw = this->argSearch(&cmd_args, "-a");
    int gen_sw = this->argSearch(&cmd_args, "-g");
    int spc_sw = this->argSearch(&cmd_args, "-n");
    int rem_sw = this->argSearch(&cmd_args, "-r");

    // Add ssid
    if (add_sw != -1) {
      // Generate random
      if (gen_sw != -1) {
        int gen_count = cmd_args.get(gen_sw + 1).toInt();
        wifi_scan_obj.generateSSIDs(gen_count);
      }
      // Add specific
      else if (spc_sw != -1) {
        String essid = cmd_args.get(spc_sw + 1);
        wifi_scan_obj.addSSID(essid);
      } else {
        Serial.println("You did not specify how to add SSIDs");
      }
    }
    // Remove SSID
    else if (rem_sw != -1) {
      int index = cmd_args.get(rem_sw + 1).toInt();
      if (!this->inRange(ssids->size(), index)) {
        Serial.println("Index not in range: " + (String)index);
        return;
      }
      ssids->remove(index);
    } else {
      Serial.println("You did not specify whether to add or remove SSIDs");
      return;
    }
  }
  // Join WiFi
  /*else if (cmd_args.get(0) == JOINWIFI_CMD) {
    int n_sw = this->argSearch(&cmd_args, "-n"); // name
    int a_sw = this->argSearch(&cmd_args, "-a"); // access point
    int s_sw = this->argSearch(&cmd_args, "-s"); // ssid
    int p_sw = this->argSearch(&cmd_args, "-p");

    String essid = "";
    String pwx = "";

    if (s_sw != -1) {
      int index = cmd_args.get(s_sw + 1).toInt();
      if (!this->inRange(ssids->size(), index)) {
        Serial.println("Index not in range: " + (String)index);
        return;
      }
      essid = ssids->get(index).essid;
    } else if (a_sw != -1) {
      int index = cmd_args.get(a_sw + 1).toInt();
      if (!this->inRange(access_points->size(), index)) {
        Serial.println("Index not in range: " + (String)index);
        return;
      }
      essid = access_points->get(index).essid;
    } else if (n_sw != -1) {
      essid = cmd_args.get(n_sw + 1);
    } else {
      Serial.println("You must specify an access point or ssid");
      return;
    }

    if (p_sw != -1) {
      pwx = cmd_args.get(p_sw + 1);
    }
    Serial.println("Attempting to join WiFi with ssid " + (String)essid);
    wifi_scan_obj.joinWiFi(essid, pwx);
  }*/
}
