0xMartin/TweenWave/Firmware/src/utils.h

#ifndef utils_h
#define utils_h

#include <Arduino.h>
#include <WiFi.h>
#include <vector>

#include "configs.h"

#include "esp_heap_caps.h"

struct mac_addr {
  unsigned char bytes[6];
};

struct Station {
  uint8_t mac[6];
  bool selected;
  uint16_t packets;
  uint16_t ap;
};

struct ProbeReqSsid {
  String essid;
  bool selected;
  uint8_t requests;
};

const char apple_ouis[][9] PROGMEM = {
    "00:17:F2", "00:1E:C2", "00:26:08", "F8:1E:DF", "BC:92:6B", "28:E0:2C",
    "3C:07:54", "7C:D1:C3", "DC:A9:04", "F0:D1:A9", "C0:2C:5C", "00:03:93",
    "00:03:94", "00:03:95", "00:03:96", "00:03:97", "00:03:98", "00:03:99",
    "00:03:9A", "00:03:9B", "00:03:9C", "00:03:9D", "00:03:9E", "00:03:9F",
    "00:03:A0", "00:03:A1", "00:03:A2", "00:03:A3", "00:03:A4", "00:03:A5",
    "00:03:A6", "00:03:A7", "00:03:A8", "00:03:A9", "00:03:AA", "00:03:AB",
    "00:03:AC", "00:03:AD", "00:03:AE", "00:03:AF", "00:03:B0", "00:03:B1",
    "00:03:B2", "00:03:B3", "00:03:B4", "00:03:B5", "00:03:B6", "00:03:B7",
    "00:03:B8", "00:03:B9", "00:03:BA", "00:03:BB", "00:03:BC", "00:03:BD",
    "00:03:BE", "00:03:BF", "00:03:C0", "00:03:C1", "00:03:C2", "00:03:C3",
    "00:03:C4", "00:03:C5", "00:03:C6", "00:03:C7", "00:03:C8", "00:03:C9",
    "00:03:CA", "00:03:CB", "00:03:CC", "00:03:CD", "00:03:CE", "00:03:CF",
    "00:03:D0", "00:03:D1", "00:03:D2", "00:03:D3", "00:03:D4", "00:03:D5",
    "00:03:D6", "00:03:D7", "00:03:D8", "00:03:D9", "00:03:DA", "00:03:DB",
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
    "D0:31:AA", "E0:4F:02", "F0:3B:94"};

const char sony_ouis[][9] PROGMEM = {"00:19:C5", "00:1B:59", "00:1E:DC",
                                     "10:68:3F", "54:42:49", "A8:E3:EE",
                                     "B8:F9:34", "CC:5D:4E", "E8:89:2F"};

const char tplink_ouis[][9] PROGMEM = {
    "00:31:92", "00:5F:67", "10:27:F5", "14:EB:B6", "1C:61:B4", "20:36:26",
    "28:87:BA", "30:DE:4B", "34:60:F9", "3C:52:A1", "40:ED:00", "48:22:54",
    "50:91:E3", "54:AF:97", "5C:62:8B", "5C:A6:E6", "5C:E9:31", "60:A4:B7",
    "68:7F:F0", "6C:5A:B0", "78:8C:B5", "7C:C2:C6", "9C:53:22", "9C:A2:F4",
    "A8:42:A1", "AC:15:A2", "B0:A7:B9", "B4:B0:24", "C0:06:C3", "CC:68:B6",
    "E8:48:B8", "F0:A7:31"};

const char xiaomi_ouis[][9] PROGMEM = {"04:CF:8C", "18:59:36", "38:1A:2D",
                                       "64:B4:73", "78:02:F8", "90:4E:91",
                                       "C4:0B:CB", "D0:DB:32"};

inline uint8_t getDRAMUsagePercent() {
  // size_t total = heap_caps_get_total_size(MALLOC_CAP_8BIT);
  // size_t free = heap_caps_get_free_size(MALLOC_CAP_8BIT);
  size_t free = ESP.getFreeHeap();
  size_t total = ESP.getHeapSize();

  if (total == 0)
    return 0; // Avoid division by zero

  size_t used = total - free;
  uint8_t percent = (used * 100) / total;
  return percent;
}

#ifdef HAS_PSRAM
inline uint8_t getPSRAMUsagePercent() {
  // size_t total = heap_caps_get_total_size(MALLOC_CAP_SPIRAM);
  // size_t free  = heap_caps_get_free_size(MALLOC_CAP_SPIRAM);

  size_t total = ESP.getPsramSize();
  size_t free = ESP.getFreePsram();

  if (total == 0)
    return 0; // Avoid division by zero or PSRAM not available

  size_t used = total - free;
  uint8_t percent = (used * 100) / total;
  return percent;
}
#endif

inline String byteArrayToHexString(const std::vector<uint8_t> &byteArray) {
  String result;

  for (size_t i = 0; i < byteArray.size(); i++) {
    // Append the byte in "0xXX" format
    result += "0x";
    if (byteArray[i] < 0x10) {
      result += "0"; // Add leading zero for single-digit hex values
    }
    result += String(byteArray[i], HEX);

    // Add a space between bytes, but not at the end
    if (i < byteArray.size() - 1) {
      result += " ";
    }
  }

  return result;
}

inline std::vector<uint8_t> hexStringToByteArray(const String &hexString) {
  std::vector<uint8_t> byteArray;

  // Split the input string by spaces
  int startIndex = 0;
  while (startIndex < hexString.length()) {
    // Find the next space or end of string
    int spaceIndex = hexString.indexOf(' ', startIndex);

    // If no space is found, process the last token
    if (spaceIndex == -1) {
      spaceIndex = hexString.length();
    }

    // Extract the "0xXX" part
    String byteString = hexString.substring(startIndex, spaceIndex);

    // Convert "0xXX" to an integer and store it in the vector
    if (byteString.startsWith("0x") || byteString.startsWith("0X")) {
      uint8_t byte = strtol(byteString.c_str() + 2, nullptr, 16);
      byteArray.push_back(byte);
    }

    // Move the start index to the next byte
    startIndex = spaceIndex + 1;
  }

  return byteArray;
}

inline void generateRandomName(char *name, size_t length) {
  static const char alphabet[] = "abcdefghijklmnopqrstuvwxyz";

  // Generate the first character as uppercase
  name[0] = 'A' + (rand() % 26);

  // Generate the remaining characters as lowercase
  for (size_t i = 1; i < length - 1; ++i) {
    name[i] = alphabet[rand() % (sizeof(alphabet) - 1)];
  }
  name[length - 1] = '\0'; // Null-terminate the string
}

inline const char *generateRandomName() {
  const char *charset = "abcdefghijklmnopqrstuvwxyzABCDEFGHIJKLMNOPQRSTUVWXYZ";
  int len = rand() % 10 + 1; // Generate a random length between 1 and 10
  char *randomName = (char *)malloc(
      (len + 1) * sizeof(char)); // Allocate memory for the random name
  for (int i = 0; i < len; ++i) {
    randomName[i] =
        charset[rand() %
                strlen(charset)]; // Select random characters from the charset
  }
  randomName[len] = '\0'; // Null-terminate the string
  return randomName;
}

inline void generateRandomMac(uint8_t *mac) {
  // Set the locally administered bit and unicast bit for the first byte
  mac[0] =
      0x02; // The locally administered bit is the second least significant bit

  // Generate the rest of the MAC address
  for (int i = 1; i < 6; i++) {
    mac[i] = random(0, 255);
  }
}

inline String macToString(const Station &station) {
  char macStr[18]; // 6 pairs of hex digits + 5 colons + null terminator
  snprintf(macStr, sizeof(macStr), "%02X:%02X:%02X:%02X:%02X:%02X",
           station.mac[0], station.mac[1], station.mac[2], station.mac[3],
           station.mac[4], station.mac[5]);
  return String(macStr);
}

inline String macToString(uint8_t macAddr[6]) {
  char macStr[18]; // 17 characters for "XX:XX:XX:XX:XX:XX" + 1 null terminator
  snprintf(macStr, sizeof(macStr), "%02X:%02X:%02X:%02X:%02X:%02X", macAddr[0],
           macAddr[1], macAddr[2], macAddr[3], macAddr[4], macAddr[5]);
  return String(macStr);
}

inline void convertMacStringToUint8(const String &macStr, uint8_t macAddr[6]) {
  // Ensure the input string is in the format "XX:XX:XX:XX:XX:XX"
  if (macStr.length() != 17) {
    Serial.println("Invalid MAC address format");
    return;
  }

  // Parse the MAC address string and fill the uint8_t array
  for (int i = 0; i < 6; i++) {
    macAddr[i] = (uint8_t)strtol(macStr.substring(i * 3, i * 3 + 2).c_str(),
                                 nullptr, 16);
  }
}

// Function to check if the given MAC address matches any known OUI
inline const char *getManufacturer(const char *addr) {
  static char oui[9]; // Temporary buffer for extracted OUI

  // Extract the first three bytes (OUI) from addr
  strncpy(oui, addr, 8);
  oui[8] = '\0'; // Ensure null termination

  // Convert the addr (OUI) to lowercase
  for (int i = 0; i < 8; i++) {
    oui[i] = tolower(oui[i]);
  }

// Helper macro to check against an array stored in PROGMEM
#define CHECK_OUI(manufacturer, list)                                          \
  for (uint8_t i = 0; i < sizeof(list) / sizeof(list[0]); i++) {               \
    char storedOUI[9];                                                         \
    strcpy_P(storedOUI, list[i]);                                              \
    /* Convert the stored OUI to lowercase */                                  \
    for (int j = 0; j < 8; j++) {                                              \
      storedOUI[j] = tolower(storedOUI[j]);                                    \
    }                                                                          \
    if (strcmp(oui, storedOUI) == 0)                                           \
      return manufacturer;                                                     \
  }

  // Check against known manufacturers
  CHECK_OUI("Apple", apple_ouis);
  CHECK_OUI("Asus", asus_ouis);
  CHECK_OUI("Belkin", belkin_ouis);
  CHECK_OUI("Cisco", cisco_ouis);
  CHECK_OUI("DLink", dlink_ouis);
  CHECK_OUI("Google", google_ouis);
  CHECK_OUI("Huawei", huawei_ouis);
  CHECK_OUI("LG", lg_ouis);
  CHECK_OUI("Linksys", linksys_ouis);
  CHECK_OUI("Netgear", netgear_ouis);
  CHECK_OUI("OnePlus", oneplus_ouis);
  CHECK_OUI("Samsung", samsung_ouis);
  CHECK_OUI("Sony", sony_ouis);
  CHECK_OUI("TP-Link", tplink_ouis);
  CHECK_OUI("Xiaomi", xiaomi_ouis);

  return ""; // Return "Unknown" if no match is found
}

inline String replaceOUIWithManufacturer(const char *sta_addr) {
  const char *manufacturer = getManufacturer(sta_addr);

  if (manufacturer == nullptr || strlen(manufacturer) == 0) {
    return String(sta_addr); // Return original if no manufacturer found
  }

  // Skip the first 8 characters (3 bytes and 2 colons)
  const char *mac_suffix = sta_addr + 8;

  // Construct the new address: manufacturer + the remaining MAC address (after
  // the first 3 bytes)
  return String(manufacturer) + mac_suffix;
}

inline IPAddress getNextIP(IPAddress currentIP, IPAddress subnetMask) {
  // Convert IPAddress to uint32_t
  uint32_t ipInt = (currentIP[0] << 24) | (currentIP[1] << 16) |
                   (currentIP[2] << 8) | currentIP[3];
  uint32_t maskInt = (subnetMask[0] << 24) | (subnetMask[1] << 16) |
                     (subnetMask[2] << 8) | subnetMask[3];

  uint32_t networkBase = ipInt & maskInt;
  uint32_t broadcast = networkBase | ~maskInt;

  uint32_t nextIP = ipInt + 1;

  if (nextIP <= networkBase) {
    nextIP = networkBase + 1;
  }
  if (nextIP >= broadcast) {
    return IPAddress(0, 0, 0, 0); // no more IPs
  }

  return IPAddress((nextIP >> 24) & 0xFF, (nextIP >> 16) & 0xFF,
                   (nextIP >> 8) & 0xFF, nextIP & 0xFF);
}

inline IPAddress getPrevIP(IPAddress currentIP, IPAddress subnetMask,
                    uint16_t stepsBack) {
  // Convert IPAddress to uint32_t
  uint32_t ipInt = (currentIP[0] << 24) | (currentIP[1] << 16) |
                   (currentIP[2] << 8) | currentIP[3];
  uint32_t maskInt = (subnetMask[0] << 24) | (subnetMask[1] << 16) |
                     (subnetMask[2] << 8) | subnetMask[3];

  uint32_t networkBase = ipInt & maskInt;
  uint32_t broadcast = networkBase | ~maskInt;

  uint32_t prevIP = ipInt - stepsBack;

  // Ensure prevIP is not below the usable range
  if (prevIP <= networkBase) {
    return IPAddress(0, 0, 0, 0); // No more IPs
  }

  return IPAddress((prevIP >> 24) & 0xFF, (prevIP >> 16) & 0xFF,
                   (prevIP >> 8) & 0xFF, prevIP & 0xFF);
}

inline uint16_t getNextPort(uint16_t port) { return port + 1; }

#endif
